tomvdb/hw-re-platform/documentation/resources/circuit_1-01.jpg

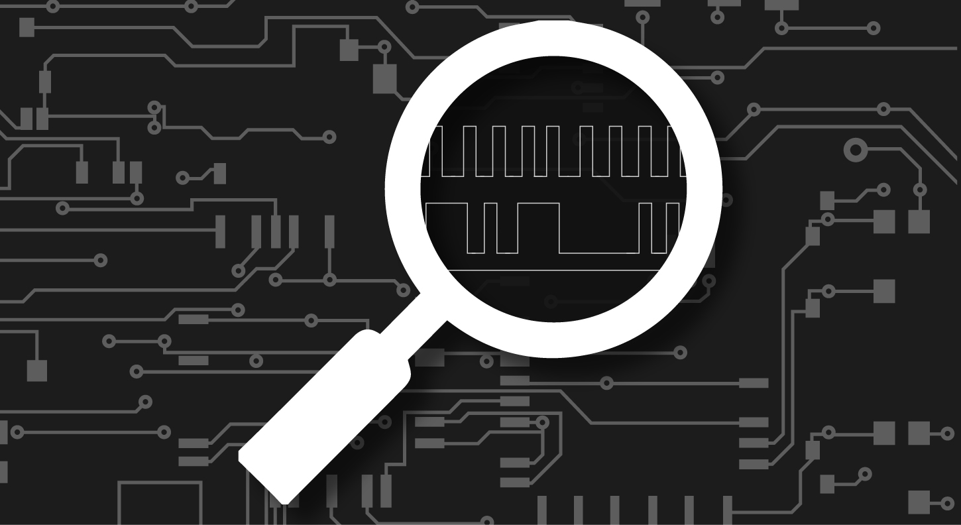
documentation/resources/circuit_1-01.jpg
